yonaguska/watchdog-timer/Docs/schematic mmbt3906.png

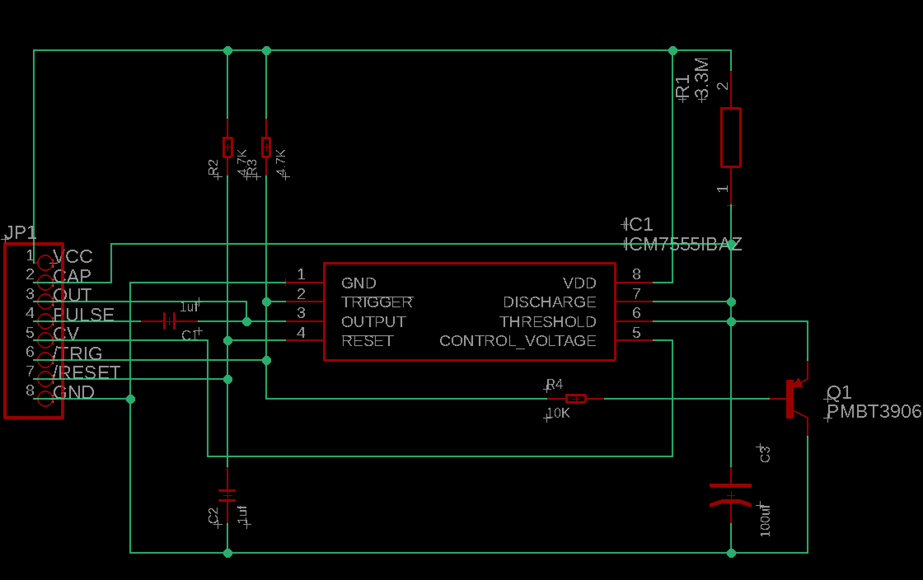
Docs/schematic mmbt3906.png
